trickydee/ultrausbt-amiga/doc/submodule-versions.md

# Submodule Versions

Recorded on 2026-05-07.

- `bluepad32`
  - SHA: `2fe3360530f8fc0f1f65dbb510a94cc73dc2a98a`
  - Version label: `4.2.0-59-g2fe3360`

- `pico-sdk`
  - SHA: `a1438dff1d38bd9c65dbd693f0e5db4b9ae91779`
  - Version label: `2.2.0`

- `tinyusb`
  - SHA: `a71cb23647d3eafd3f34b3641fd17ea49b131aec`
  - Version label: `0.20.0-250-ga71cb2364`
