trickydee/ultrausbt-amiga/doc/atari-vs-joypad-os-controller-comparison.md

# Atari IKBD vs Joypad OS Controller Implementation Comparison

**Date**: 2025-01-XX  
**Branch**: `joystickos-investigation`

## Executive Summary

**The Atari IKBD project uses a similar architecture to AmigaHID-Pico** - direct controller integration without a router system. **Joypad OS's drivers would require MORE work to integrate** because they depend on the router system. **However, Joypad OS's drivers are more mature and feature-complete**, so porting them could still be valuable.

## Atari IKBD Controller Architecture

### Structure
- **Individual controller files**: `ps3_controller.c`, `ps4_controller.c`, `switch_controller.c`, `stadia_controller.c`, `xinput.c`
- **Direct TinyUSB integration**: Controllers hook into `tuh_hid_report_received_cb()` via `hid_app_host.c`
- **VID/PID matching**: Each controller has an `is_controller(vid, pid)` function
- **Direct output**: Controllers directly map to Atari joystick ports (similar to AmigaHID-Pico)
- **No router system**: Direct control, no intermediate routing layer

### Example: PS4 Controller

```c
// ps4_controller.c
bool ps4_is_dualshock4(uint16_t vid, uint16_t pid) {
    if (vid != PS4_VENDOR_ID) return false;
    switch (pid) {
        case PS4_DS4_PID_V1:
        case PS4_DS4_PID_V2:
        case PS4_DS4_PID_DONGLE:
            return true;
        default:
            return false;
    }
}

bool ps4_process_report(uint8_t dev_addr, const uint8_t* report, uint16_t len) {
    // Parse PS4 report
    // Direct mapping to Atari joystick ports
    // No router system - direct control
}
```

### Integration Pattern

1. **Device Detection** (`hid_app_host.c`):
   ```c
   void tuh_hid_mount_cb(uint8_t dev_addr, uint8_t instance, ...) {
       uint16_t vid, pid;
       tuh_vid_pid_get(dev_addr, &vid, &pid);
       
       // Try vendor-specific controllers first
       if (ps4_is_dualshock4(vid, pid)) {
           // Allocate PS4 controller
       } else if (switch_is_controller(vid, pid)) {
           // Allocate Switch controller
       } else if (xinput_is_xbox_controller(vid, pid)) {
           // Allocate Xbox controller
       }
       // ... etc
   }
   ```

2. **Report Processing** (`hid_app_host.c`):
   ```c
   void tuh_hid_report_received_cb(uint8_t dev_addr, uint8_t instance, 
                                    uint8_t const* report, uint16_t len) {
       // Route to appropriate controller handler
       if (ps4_is_dualshock4(vid, pid)) {
           ps4_process_report(dev_addr, report, len);
       } else if (switch_is_controller(vid, pid)) {
           switch_process_report(dev_addr, report, len);
       }
       // ... etc
   }
   ```

3. **Direct Output**: Controllers directly call Atari joystick port functions (similar to AmigaHID-Pico's GPIO control)

## Joypad OS Controller Architecture

### Structure
- **Driver registry system**: All drivers registered in `hid_registry.c`
- **Router system**: Controllers submit to `router_submit_input()` instead of direct output
- **Input event structure**: Standardized `input_event_t` format
- **Player management**: Tracks which device is assigned to which player
- **Feedback system**: Rumble, LED, adaptive trigger management

### Example: DS4 Driver

```c
// sony_ds4.c
void input_sony_ds4(uint8_t dev_addr, uint8_t instance, 
                    uint8_t const* report, uint16_t len) {
    // Parse DS4 report
    input_event_t event = {
        .buttons = /* map buttons */,
        .analog[ANALOG_LX] = ds4->x,
        // ...
    };
    
    // Submit to router (NOT direct output)
    router_submit_input(&event);
}
```

## Comparison: Which is Easier to Use?

### ✅ **Atari IKBD Approach is EASIER for AmigaHID-Pico**

**Why:**
1. **Same architecture**: Direct controller → output mapping (no router)
2. **Similar integration pattern**: VID/PID matching, direct report processing
3. **No architectural changes needed**: Can copy controller code almost as-is
4. **Direct GPIO control**: Controllers can directly call Amiga GPIO functions

**Effort to port a controller from Atari IKBD:**
- Copy controller file
- Replace Atari joystick port calls with Amiga GPIO calls
- Update VID/PID matching if needed
- **Estimated: 1-2 days per controller**

### ⚠️ **Joypad OS Approach is HARDER for AmigaHID-Pico**

**Why:**
1. **Different architecture**: Router system vs direct control
2. **Dependencies**: Requires router, input_event, player management, feedback
3. **More refactoring**: Must adapt from `router_submit_input()` to direct GPIO
4. **Architectural mismatch**: Designed for different use case

**Effort to port a controller from Joypad OS:**
- Copy driver code
- Remove router dependencies
- Replace `router_submit_input()` with direct GPIO calls
- Remove player management, feedback system dependencies
- Adapt `input_event_t` to AmigaHID-Pico structures
- **Estimated: 2-3 days per controller**

## Controller Quality Comparison

### Atari IKBD Controllers

**Strengths:**
- ✅ Simple, direct implementation
- ✅ Easy to understand and modify
- ✅ No external dependencies
- ✅ Works well for basic use cases

**Weaknesses:**
- ⚠️ Less feature-complete (no motion sensors, touchpad, etc.)
- ⚠️ May have quirks or edge cases
- ⚠️ Less tested across different controller variants

### Joypad OS Controllers

**Strengths:**
- ✅ More feature-complete (motion sensors, touchpad, pressure-sensitive buttons)
- ✅ Better tested (larger user base)
- ✅ Handles more edge cases and controller variants
- ✅ Better button mapping for arcade sticks
- ✅ More mature codebase

**Weaknesses:**
- ⚠️ More complex (router dependencies)
- ⚠️ Harder to port (architectural mismatch)

## Recommendation

### Option 1: Use Atari IKBD Controllers (Easier, Faster)

**Best for:**
- Quick integration
- Basic controller support
- Minimal code changes

**Process:**
1. Copy controller files from Atari IKBD
2. Replace Atari joystick port calls with Amiga GPIO calls
3. Update VID/PID matching if needed
4. Test and adjust

**Estimated effort**: 1-2 days per controller

**Controllers available:**
- PS3 DualShock 3
- PS4 DualShock 4
- Switch Pro Controller
- Stadia Controller
- Xbox (via XInput)
- GameCube Adapter

### Option 2: Port Joypad OS Controllers (More Work, Better Features)

**Best for:**
- Advanced features (motion, touchpad, pressure-sensitive buttons)
- Better compatibility with edge cases
- More controller variants

**Process:**
1. Copy driver code from Joypad OS
2. Remove router dependencies
3. Replace `router_submit_input()` with direct GPIO calls
4. Remove player management, feedback dependencies
5. Adapt `input_event_t` to AmigaHID-Pico structures

**Estimated effort**: 2-3 days per controller

**Additional benefit**: Could adopt `input_event_t` structure for cleaner code

### Option 3: Hybrid Approach (Recommended)

**Best of both worlds:**

1. **Start with Atari IKBD controllers** (quick wins):
   - PS3, PS4, Switch, Stadia, Xbox
   - Easy to port, works immediately
   - **Effort: 1-2 weeks for all controllers**

2. **Port high-value Joypad OS features** (if needed):
   - DualSense (PS5) - not in Atari IKBD
   - Motion sensor support (if needed)
   - Touchpad support (if needed)
   - Better arcade stick handling
   - **Effort: 2-3 days per feature**

3. **Adopt `input_event_t` structure** (optional, but recommended):
   - Cleaner code
   - Easier to add new controllers
   - **Effort: 2-3 days**

## Specific Controller Comparison

### PS4 DualShock 4

**Atari IKBD** (`ps4_controller.c`):
- ✅ Simple, direct implementation
- ✅ Basic button/analog support
- ⚠️ No touchpad support
- ⚠️ No motion sensor support
- ⚠️ No pressure-sensitive buttons

**Joypad OS** (`sony_ds4.c`):
- ✅ Touchpad support
- ✅ Motion sensor support (gyro/accel)
- ✅ Pressure-sensitive buttons
- ✅ Better arcade stick compatibility
- ⚠️ More complex (router dependencies)

**Verdict**: Atari IKBD is easier to port, but Joypad OS has more features. **Start with Atari IKBD, port Joypad OS features if needed.**

### Switch Pro Controller

**Atari IKBD** (`switch_controller.c`):
- ✅ Full initialization sequence
- ✅ Button/analog support
- ✅ Capture/home button support
- ⚠️ No motion sensor support

**Joypad OS** (`switch_pro.c`):
- ✅ Motion sensor support
- ✅ Better initialization handling
- ✅ Joy-Con Grip support
- ⚠️ More complex

**Verdict**: Atari IKBD is good enough for basic use. **Port Joypad OS if motion sensors are needed.**

### Stadia Controller

**Atari IKBD** (`stadia_controller.c`):
- ✅ Basic implementation
- ✅ Button/analog support

**Joypad OS** (`google_stadia.c`):
- ✅ More mature implementation
- ✅ Better edge case handling

**Verdict**: Both are similar. **Atari IKBD is easier to port.**

## Conclusion

**For AmigaHID-Pico, the Atari IKBD controllers are EASIER to use** because:
1. Same architecture (direct control, no router)
2. Similar integration pattern
3. Less refactoring needed
4. Faster to port (1-2 days vs 2-3 days)

**However, Joypad OS controllers have MORE features**:
- Motion sensors
- Touchpad support
- Pressure-sensitive buttons
- Better edge case handling

**Recommended approach:**
1. **Start with Atari IKBD controllers** (quick wins, 1-2 weeks)
2. **Port Joypad OS features selectively** (if needed, 2-3 days each)
3. **Consider adopting `input_event_t` structure** (cleaner code, 2-3 days)

This gives you the best balance of speed and features.
