trickydee/ultrausbt-amiga/doc/progress-notes.md

# Progress Notes - USB Controller Integration

**Date**: 2025-01-XX  
**Branch**: `gpio_pin_mapping_pico_w_fixes-add-usb-devices-from-atari`  
**Version**: 1.0.40

## Current Status

### ✅ Completed

1. **PS3 DualShock 3 Controller** (VID: 0x054C, PID: 0x0268)
   - ✅ Integrated from Atari IKBD codebase
   - ✅ Mapped to Joystick Port 2
   - ✅ Full button and direction support
   - ✅ Tested and working

2. **PS4 DualShock 4 Controller** (VID: 0x054C, PIDs: 0x05C4, 0x09CC, 0x0BA0)
   - ✅ Integrated from Atari IKBD codebase
   - ✅ Mapped to Joystick Port 2
   - ✅ Reduced deadzone from 50 to 20 for better sensitivity
   - ✅ Fixed stick calculation type (int8_t → int16_t) to prevent overflow
   - ✅ Full button and direction support
   - ✅ Tested and working (after cable reseating - hardware issue resolved)

### 🔧 Current Issues / Notes

1. **Debug Messages Still Included**
   - Extensive debug output added to PS4 controller for troubleshooting
   - GPIO state change messages in `joystick_port2.c`
   - Direction calculation messages in `ps4_controller.c`
   - **TODO**: Remove debug messages in future commit

2. **USB vs Bluetooth Gamepad Allocation**
   - Currently: First USB gamepad → Port 2, First Bluetooth gamepad → Port 2
   - No conflict resolution strategy yet
   - **TODO**: Design allocation strategy (priority, round-robin, user selection, etc.)

### 📋 Next Steps

1. **Nintendo Switch Pro Controller** (VID: 0x057E, PID: 0x2009)
   - Next controller to implement
   - Requires initialization sequence (1-second delay after mount)
   - Similar structure to PS4, should be straightforward
   - Estimated effort: 1-2 days

2. **Remaining Controllers** (in order):
   - Google Stadia Controller (VID: 0x18D1, PID: 0x9400) - Easy
   - Xbox Controllers (VID: 0x045E, 7 PIDs) - Medium effort (XInput protocol)
   - Nintendo GameCube Adapter (VID: 0x057E, PID: 0x0337) - Complex (4-port)

### 📝 Code Changes Summary

**Files Modified:**
- `src/main.c` - Version bumped to 1.0.40
- `src/display/display.c` - Version bumped to 1.0.40
- `src/usb_hid.c` - Removed unused `last_report` variable, integrated PS3/PS4 detection
- `src/usb_controllers/ps3_controller.c` - PS3 controller implementation
- `src/usb_controllers/ps3_controller.h` - PS3 controller header
- `src/usb_controllers/ps4_controller.c` - PS4 controller implementation (with debug)
- `src/usb_controllers/ps4_controller.h` - PS4 controller header
- `src/platform/amiga/joystick_port2.c` - Added GPIO debug messages
- `src/bluepad32_platform.c` - Fixed strncpy warnings (snprintf with %.*s)
- `src/CMakeLists.txt` - Added PS3 and PS4 controller source files

**Integration Points:**
- `tuh_hid_mount_cb()` in `usb_hid.c` - Detects PS3/PS4 controllers
- `tuh_hid_report_received_cb()` in `usb_hid.c` - Routes reports to PS3/PS4 handlers
- `tuh_hid_umount_cb()` in `usb_hid.c` - Handles disconnection

### 🐛 Known Issues / Resolved

1. **PS4 Controller Not Working Initially**
   - **Issue**: GPIO updates happening but no movement/buttons
   - **Root Cause**: Hardware issue (cable connection)
   - **Resolution**: Reseated cables, now working perfectly
   - **Lesson**: GPIO code was correct, issue was hardware

2. **Build Warnings Fixed**
   - Unused variable `last_report` in `handle_event_mouse()` - Removed
   - `strncpy` truncation warnings in `bluepad32_platform.c` - Fixed with `snprintf`

3. **Version Number Sync**
   - Fixed mismatch between `main.c` (1.0.39) and `display.c` fallback (1.0.37)
   - Both now synchronized to 1.0.40

### 📚 Reference Documentation

- `doc/atari-controllers-available.md` - List of available controllers from Atari IKBD
- `doc/usb-controllers-integration-plan.md` - Integration plan and steps
- `doc/atari-vs-joypad-os-controller-comparison.md` - Architecture comparison

### 🔄 Git Status

**Note**: Last commit attempt may not have completed. Verify with:
```bash
git status
git log --oneline -1
```

**Intended Commit Message:**
```
Add PS4 DualShock 4 USB controller support (v1.0.40)

- Integrated PS4 DualShock 4 controller from Atari IKBD codebase
- Reduced deadzone from 50 to 20 for better analog stick sensitivity
- Fixed stick calculation type (int8_t -> int16_t) to prevent overflow
- Added extensive debug output for GPIO state changes and direction calculations
- Fixed unused variable warnings (removed last_report from handle_event_mouse)
- Fixed strncpy warnings by using snprintf with %.*s format
- Version bumped to 1.0.40

Note: Debug messages are still included for troubleshooting and will be removed in a future commit.
```

### 🎯 Immediate Next Actions (After Restart)

1. Verify git commit status
2. Begin Switch Pro Controller implementation
3. Copy `switch_controller.c` and `switch_controller.h` from Atari IKBD
4. Adapt to Amiga GPIO calls (replace Atari functions)
5. Integrate into `usb_hid.c`
6. Test and adjust deadzone if needed
